ysoldak/fpvc-gadget/media/BatteryDimensions.jpg

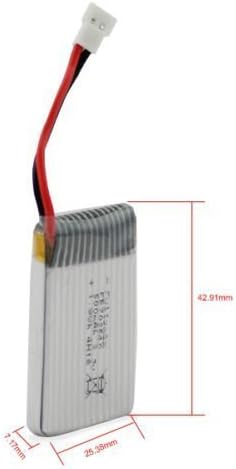
media/BatteryDimensions.jpg
